jacksterb1234/Smart_Watch/Software/src/power_manager.h

/*
 * SPDX-License-Identifier: Apache-2.0
 */

#ifndef SMARTWATCH_POWER_MANAGER_H_
#define SMARTWATCH_POWER_MANAGER_H_

int power_manager_init(void);
void power_manager_notify_user_activity(void);

#endif /* SMARTWATCH_POWER_MANAGER_H_ */
